climent/atreyu/pictures/PXL_20210609_174713826.jpg

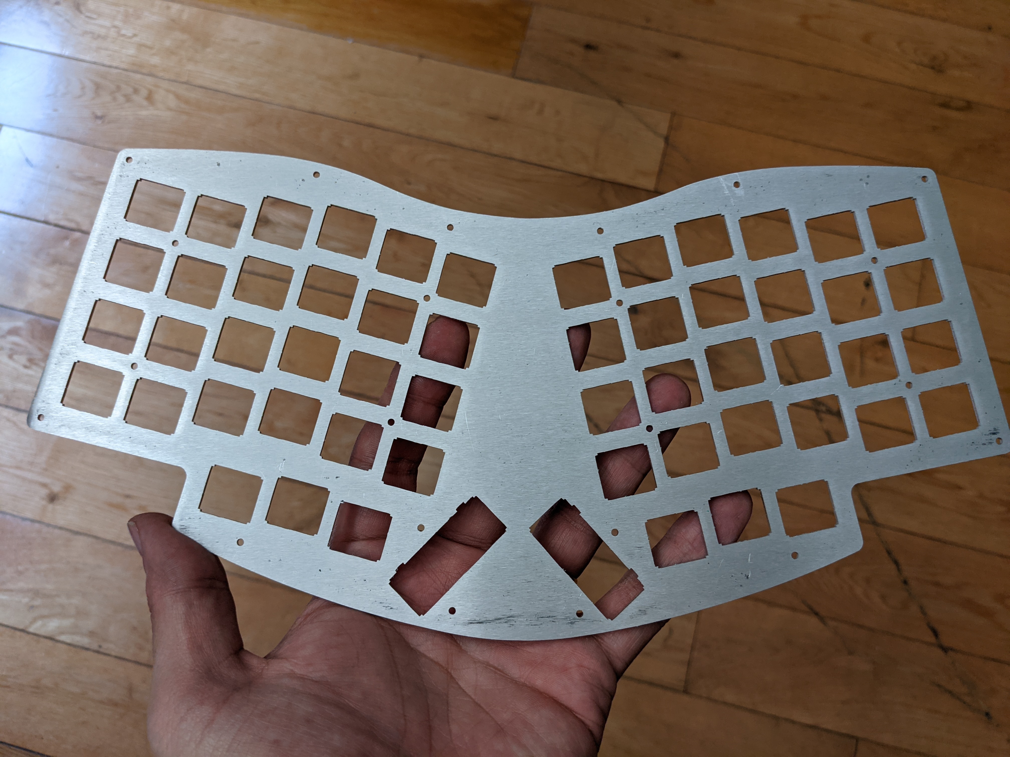
pictures/PXL_20210609_174713826.jpg
