climent/atreyu/pcb/v2-choc/v2-choc.kicad_sch

## KiCad design pcb/v2-choc/v2-choc.kicad_sch (2023-01-02)

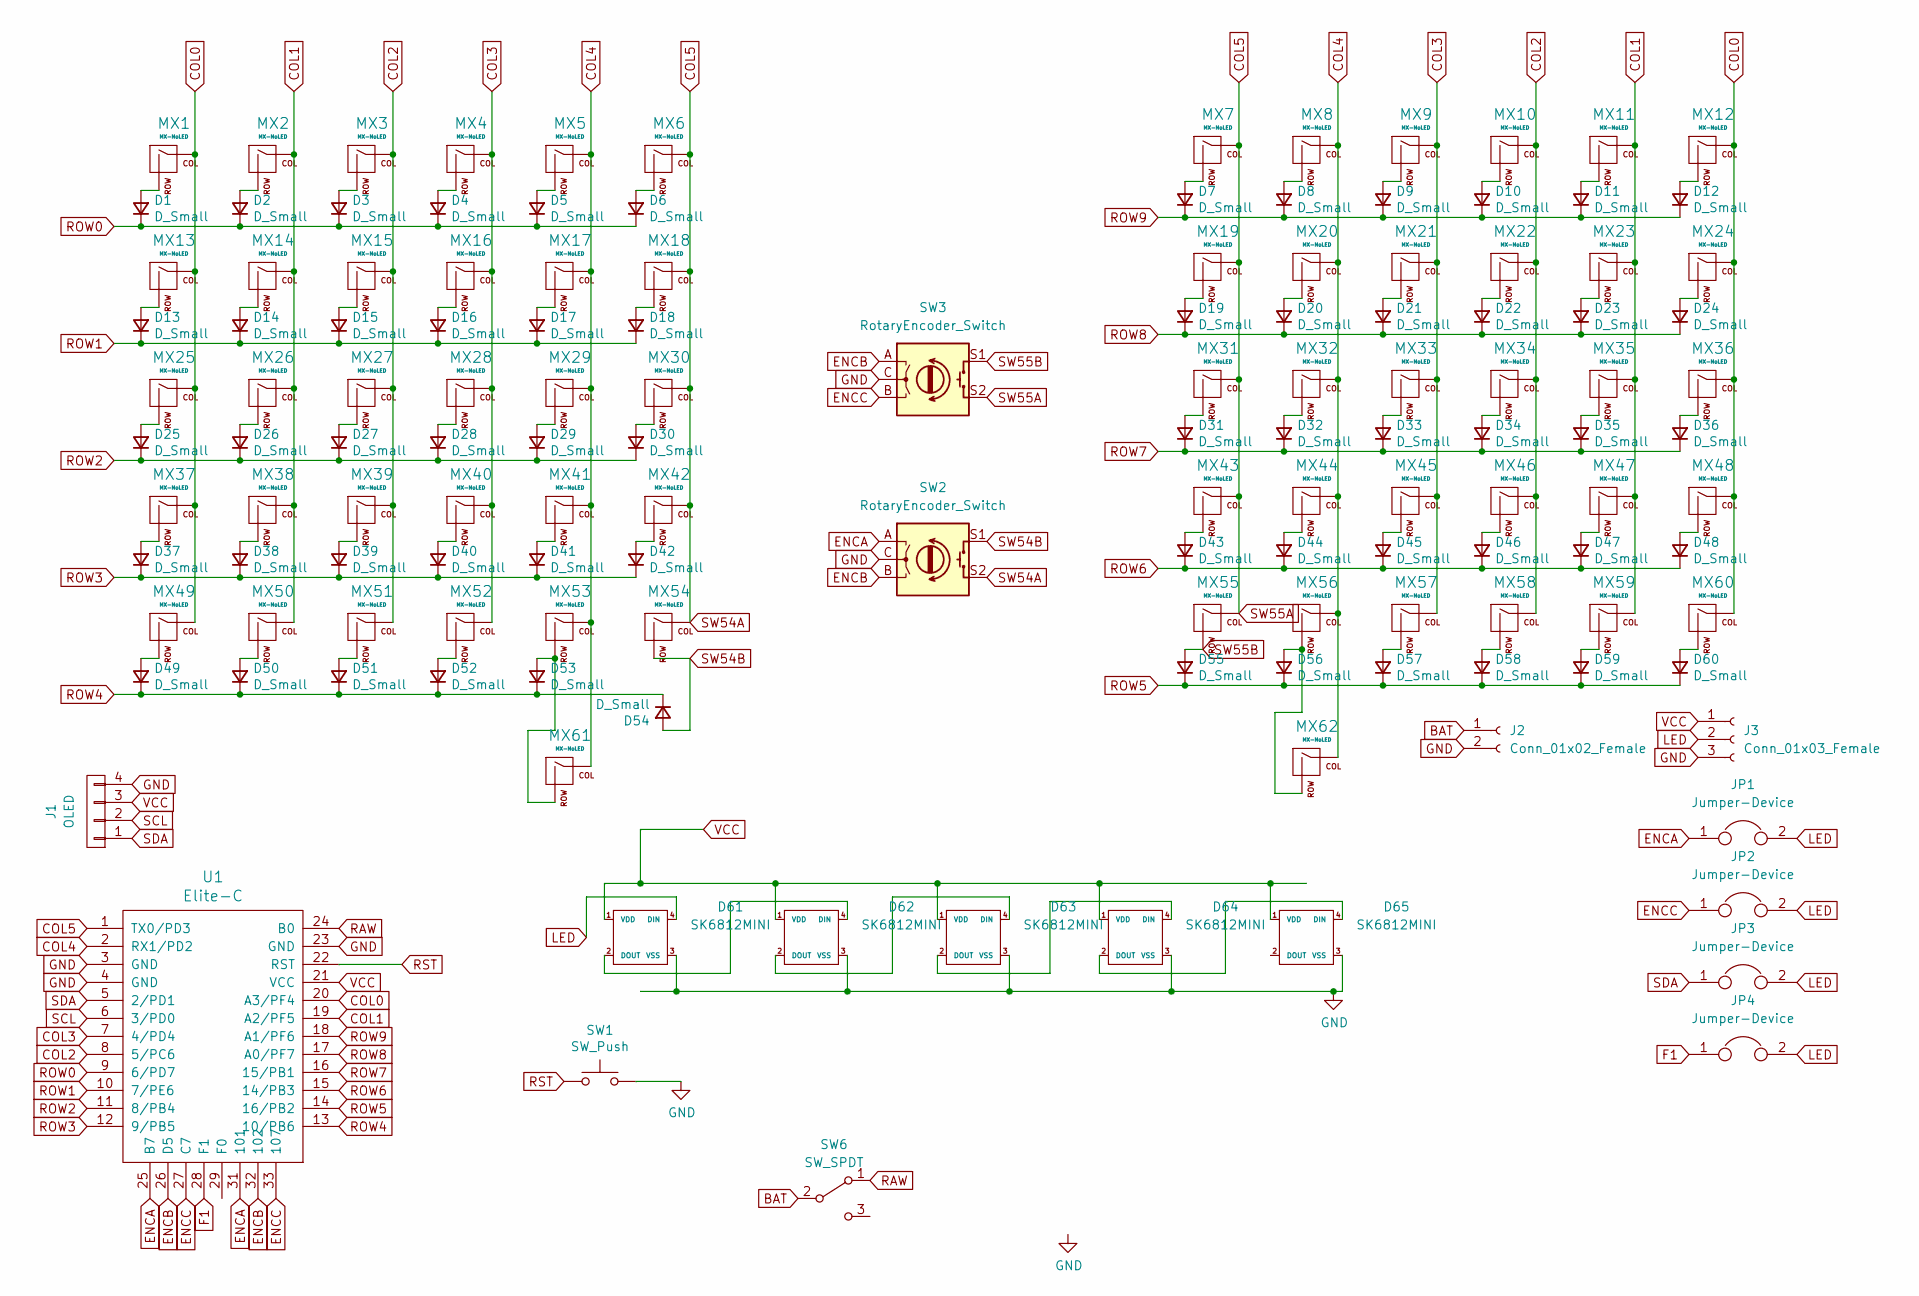
[picture p9: schematic v2-choc.kicad_sch]

Parts:
D1, D2, D3, D4, D5, D6, D7, D8, D9, D10, D11, D12, D13, D14, D15, D16, D17, D18, D19, D20, D21, D22, D23, D24, D25, D26, D27, D28, D29, D30, D31, D32, D33, D34, D35, D36, D37, D38, D39, D40, D41, D42, D43, D44, D45, D46, D47, D48, D49, D50, D51, D52, D53, D54, D55, D56, D57, D58, D59, D60: D_Small; D3_hybrid_common_hole_connected_fix
D61, D62, D63, D64, D65: SK6812MINI; YS-SK6812MINI-E
J1: OLED; PinHeader_1x04_P2.54mm_Vertical
J2: Conn_01x02_Female; PinHeader_1x02_P2.54mm_Vertical
J3: Conn_01x03_Female; PinHeader_1x03_P2.54mm_Vertical
JP1, JP2, JP3, JP4: Jumper-Device; SolderJumper-2_P1.3mm_Open_RoundedPad1.0x1.5mm
MX1, MX2, MX3, MX4, MX5, MX6, MX7, MX8, MX9, MX10, MX11, MX12, MX13, MX14, MX15, MX16, MX17, MX18, MX19, MX20, MX21, MX22, MX23, MX24, MX25, MX26, MX27, MX28, MX29, MX30, MX31, MX32, MX33, MX34, MX35, MX36, MX37, MX38, MX39, MX40, MX41, MX42, MX43, MX44, MX45, MX46, MX47, MX48, MX49, MX50, MX51, MX52, MX53, MX54, MX55, MX56, MX57, MX58, MX59, MX60, MX61, MX62: MX-NoLED; Choc_Hotswap_Solder_18x17
SW1: SW_Push; PushSwitch
SW2, SW3: RotaryEncoder_Switch; RotaryEncoder_EC11
SW6: SW_SPDT; Switch_MSK-12C01-07
U1: Elite-C

Connections:
BAT: J2.1, SW6.2 (B)
COL0: MX1.1 (COL), MX12.1 (COL), MX13.1 (COL), MX24.1 (COL), MX25.1 (COL), MX36.1 (COL), MX37.1 (COL), MX48.1 (COL), MX49.1 (COL), MX60.1 (COL), U1.20 (A3/PF4)
COL1: MX2.1 (COL), MX11.1 (COL), MX14.1 (COL), MX23.1 (COL), MX26.1 (COL), MX35.1 (COL), MX38.1 (COL), MX47.1 (COL), MX50.1 (COL), MX59.1 (COL), U1.19 (A2/PF5)
COL2: MX3.1 (COL), MX10.1 (COL), MX15.1 (COL), MX22.1 (COL), MX27.1 (COL), MX34.1 (COL), MX39.1 (COL), MX46.1 (COL), MX51.1 (COL), MX58.1 (COL), U1.8 (5/PC6)
COL3: MX4.1 (COL), MX9.1 (COL), MX16.1 (COL), MX21.1 (COL), MX28.1 (COL), MX33.1 (COL), MX40.1 (COL), MX45.1 (COL), MX52.1 (COL), MX57.1 (COL), U1.7 (4/PD4)
COL4: MX5.1 (COL), MX8.1 (COL), MX17.1 (COL), MX20.1 (COL), MX29.1 (COL), MX32.1 (COL), MX41.1 (COL), MX44.1 (COL), MX53.1 (COL), MX56.1 (COL), MX61.1 (COL), MX62.1 (COL), U1.2 (RX1/PD2)
COL5: MX6.1 (COL), MX7.1 (COL), MX18.1 (COL), MX19.1 (COL), MX30.1 (COL), MX31.1 (COL), MX42.1 (COL), MX43.1 (COL), MX54.1 (COL), MX55.1 (COL), SW2.S2, SW3.S2, U1.1 (TX0/PD3)
ENCA: JP1.1, SW2.A, U1.25 (B7), U1.31 (101)
ENCB: SW2.B, SW3.A, U1.26 (D5), U1.32 (102)
ENCC: JP2.1, SW3.B, U1.27 (C7), U1.33 (107)
F1: JP4.1, U1.28 (F1)
GND: D61.3 (VSS), D62.3 (VSS), D63.3 (VSS), D64.3 (VSS), D65.3 (VSS), J1.4, J2.2, J3.3, SW1.2, SW2.C, SW3.C, U1.3 (GND), U1.4 (GND), U1.23 (GND)
LED: D61.4 (DIN), J3.2, JP1.2, JP2.2, JP3.2, JP4.2
unnamed: D1.2 (A), MX1.2 (ROW)
unnamed: D2.2 (A), MX2.2 (ROW)
unnamed: D3.2 (A), MX3.2 (ROW)
unnamed: D4.2 (A), MX4.2 (ROW)
unnamed: D5.2 (A), MX5.2 (ROW)
unnamed: D6.2 (A), MX6.2 (ROW)
unnamed: D7.2 (A), MX7.2 (ROW)
unnamed: D8.2 (A), MX8.2 (ROW)
unnamed: D9.2 (A), MX9.2 (ROW)
unnamed: D10.2 (A), MX10.2 (ROW)
unnamed: D11.2 (A), MX11.2 (ROW)
unnamed: D12.2 (A), MX12.2 (ROW)
unnamed: D13.2 (A), MX13.2 (ROW)
unnamed: D14.2 (A), MX14.2 (ROW)
unnamed: D15.2 (A), MX15.2 (ROW)
unnamed: D16.2 (A), MX16.2 (ROW)
unnamed: D17.2 (A), MX17.2 (ROW)
unnamed: D18.2 (A), MX18.2 (ROW)
unnamed: D19.2 (A), MX19.2 (ROW)
unnamed: D20.2 (A), MX20.2 (ROW)
unnamed: D21.2 (A), MX21.2 (ROW)
unnamed: D22.2 (A), MX22.2 (ROW)
unnamed: D23.2 (A), MX23.2 (ROW)
unnamed: D24.2 (A), MX24.2 (ROW)
unnamed: D25.2 (A), MX25.2 (ROW)
unnamed: D26.2 (A), MX26.2 (ROW)
unnamed: D27.2 (A), MX27.2 (ROW)
unnamed: D28.2 (A), MX28.2 (ROW)
unnamed: D29.2 (A), MX29.2 (ROW)
unnamed: D30.2 (A), MX30.2 (ROW)
unnamed: D31.2 (A), MX31.2 (ROW)
unnamed: D32.2 (A), MX32.2 (ROW)
unnamed: D33.2 (A), MX33.2 (ROW)
unnamed: D34.2 (A), MX34.2 (ROW)
unnamed: D35.2 (A), MX35.2 (ROW)
unnamed: D36.2 (A), MX36.2 (ROW)
unnamed: D37.2 (A), MX37.2 (ROW)
unnamed: D38.2 (A), MX38.2 (ROW)
unnamed: D39.2 (A), MX39.2 (ROW)
unnamed: D40.2 (A), MX40.2 (ROW)
unnamed: D41.2 (A), MX41.2 (ROW)
unnamed: D42.2 (A), MX42.2 (ROW)
unnamed: D43.2 (A), MX43.2 (ROW)
unnamed: D44.2 (A), MX44.2 (ROW)
unnamed: D45.2 (A), MX45.2 (ROW)
unnamed: D46.2 (A), MX46.2 (ROW)
unnamed: D47.2 (A), MX47.2 (ROW)
unnamed: D48.2 (A), MX48.2 (ROW)
unnamed: D49.2 (A), MX49.2 (ROW)
unnamed: D50.2 (A), MX50.2 (ROW)
unnamed: D51.2 (A), MX51.2 (ROW)
unnamed: D52.2 (A), MX52.2 (ROW)
unnamed: D53.2 (A), MX53.2 (ROW), MX61.2 (ROW)
unnamed: D56.2 (A), MX56.2 (ROW), MX62.2 (ROW)
unnamed: D57.2 (A), MX57.2 (ROW)
unnamed: D58.2 (A), MX58.2 (ROW)
unnamed: D59.2 (A), MX59.2 (ROW)
unnamed: D60.2 (A), MX60.2 (ROW)
unnamed: D61.2 (DOUT), D62.4 (DIN)
unnamed: D62.2 (DOUT), D63.4 (DIN)
unnamed: D63.2 (DOUT), D64.4 (DIN)
unnamed: D64.2 (DOUT), D65.4 (DIN)
RAW: SW6.1 (A), U1.24 (B0)
ROW0: D1.1 (K), D2.1 (K), D3.1 (K), D4.1 (K), D5.1 (K), D6.1 (K), U1.9 (6/PD7)
ROW1: D13.1 (K), D14.1 (K), D15.1 (K), D16.1 (K), D17.1 (K), D18.1 (K), U1.10 (7/PE6)
ROW2: D25.1 (K), D26.1 (K), D27.1 (K), D28.1 (K), D29.1 (K), D30.1 (K), U1.11 (8/PB4)
ROW3: D37.1 (K), D38.1 (K), D39.1 (K), D40.1 (K), D41.1 (K), D42.1 (K), U1.12 (9/PB5)
ROW4: D49.1 (K), D50.1 (K), D51.1 (K), D52.1 (K), D53.1 (K), D54.1 (K), U1.13 (10/PB6)
ROW5: D55.1 (K), D56.1 (K), D57.1 (K), D58.1 (K), D59.1 (K), D60.1 (K), U1.14 (16/PB2)
ROW6: D43.1 (K), D44.1 (K), D45.1 (K), D46.1 (K), D47.1 (K), D48.1 (K), U1.15 (14/PB3)
ROW7: D31.1 (K), D32.1 (K), D33.1 (K), D34.1 (K), D35.1 (K), D36.1 (K), U1.16 (15/PB1)
ROW8: D19.1 (K), D20.1 (K), D21.1 (K), D22.1 (K), D23.1 (K), D24.1 (K), U1.17 (A0/PF7)
ROW9: D7.1 (K), D8.1 (K), D9.1 (K), D10.1 (K), D11.1 (K), D12.1 (K), U1.18 (A1/PF6)
RST: SW1.1, U1.22 (RST)
SCL: J1.2, U1.6 (3/PD0)
SDA: J1.1, JP3.1, U1.5 (2/PD1)
SW54B: D54.2 (A), MX54.2 (ROW), SW2.S1
SW55B: D55.2 (A), MX55.2 (ROW), SW3.S1
VCC: D61.1 (VDD), D62.1 (VDD), D63.1 (VDD), D64.1 (VDD), D65.1 (VDD), J1.3, J3.1, U1.21 (VCC)
